curiouselectric/dc_dc_controller/DC_DC_Controller Instructions/Photos/DC_DC_controller_parts.jpg

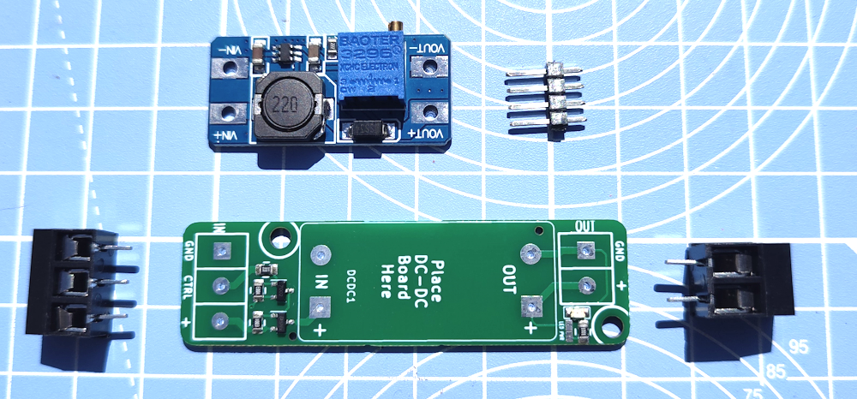
DC_DC_Controller Instructions/Photos/DC_DC_controller_parts.jpg
