curiouselectric/dc_dc_controller/DC_DC_Controller Instructions/Photos/DC_DC_controller_2.jpg

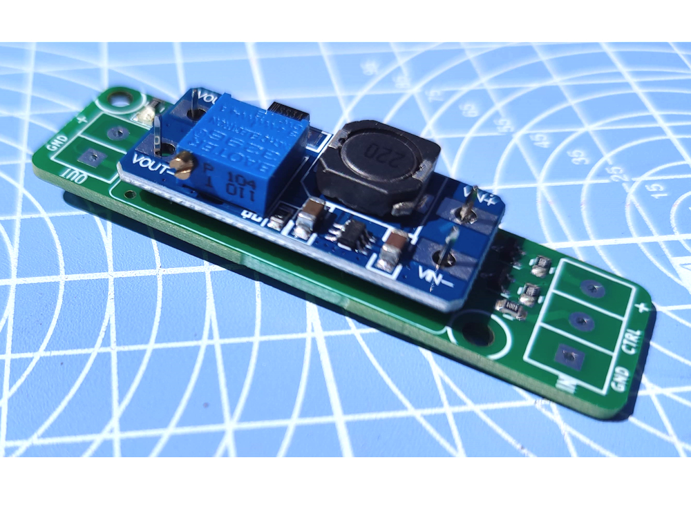
DC_DC_Controller Instructions/Photos/DC_DC_controller_2.jpg
