curiouselectric/dc_dc_controller/DC_DC_Controller Instructions/Photos/IMG_20230703_142130.jpg

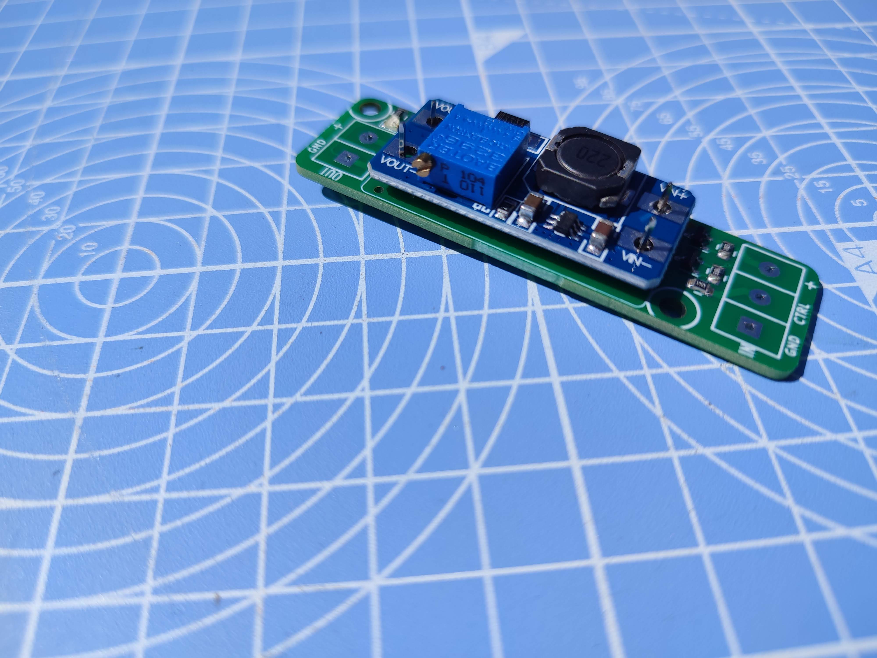
DC_DC_Controller Instructions/Photos/IMG_20230703_142130.jpg
