curiouselectric/dc_dc_controller/DC_DC_Controller Instructions/Photos/Photos for Tindie/DC_DC_controller_2_tindie.jpg

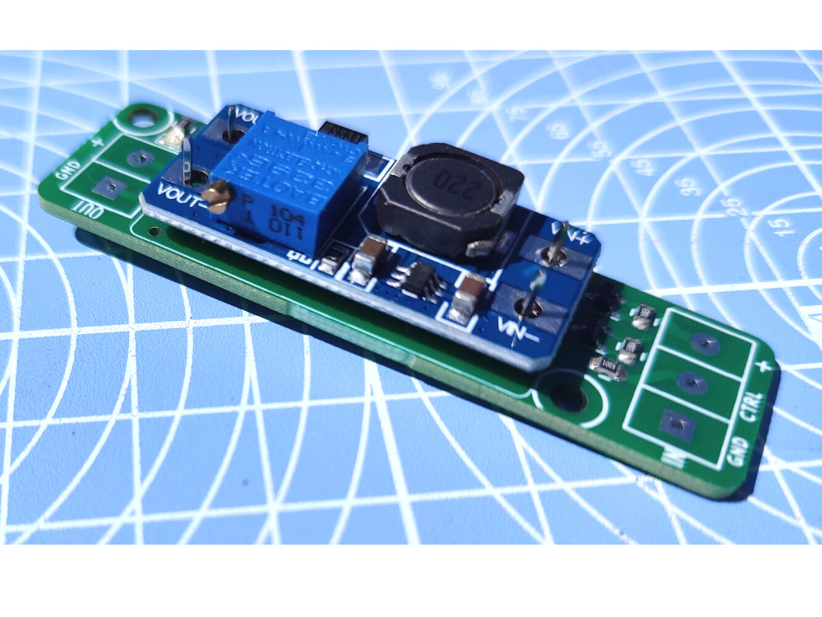
DC_DC_Controller Instructions/Photos/Photos for Tindie/DC_DC_controller_2_tindie.jpg
